nickmedina5991/mister-fuzz/simulation/FuzzFace.asc

C1: cap; 2.2µ; V=10 Irms=0 Rser=7 Lser=0 mfg="AVX" pn="TAJA225M010" type="Tantalum"
C2: cap; 22µ; V=16 Irms=0 Rser=1.6 Lser=0 mfg="AVX" pn="TAJC226K016" type="Tantalum"
C4: cap; 0.01µ
Q1: npn; 2N3904
Q2: npn; 2N3904
R1: res; 33k
R2: res; 470
R3: res; 6k
R4: res; 100k
R_fuzz_a: res; {r_fuzz*(1-fuzz_k)}
R_fuzz_b: res; {r_fuzz*fuzz_k}
R_vol_a: res; {r_vol*(1-vol_k)}
R_vol_b: res; {r_vol*vol_k}
V1: battery; 9V
V2: voltage; SINE(0 0.2 440); AC 1
Named nets: 0, OUT, IN
.param r_fuzz = 1k
.param r_vol  = 500k
.param fuzz_k = 0.99
.param vol_k  = 0.99
.step param fuzz_k list 0.01 0.25 0.5 0.75 0.99
.tran 0 200m 100m
.op
.ac dec 100 10 100k
